EdwinTSalcedo/ForestProtector/images/nighttime-confusion-matrix.png

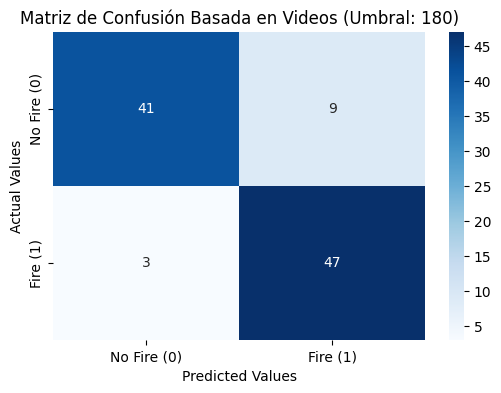
images/nighttime-confusion-matrix.png
