EdwinTSalcedo/ForestProtector/webapp/backend/scripts/captured_frames.gif

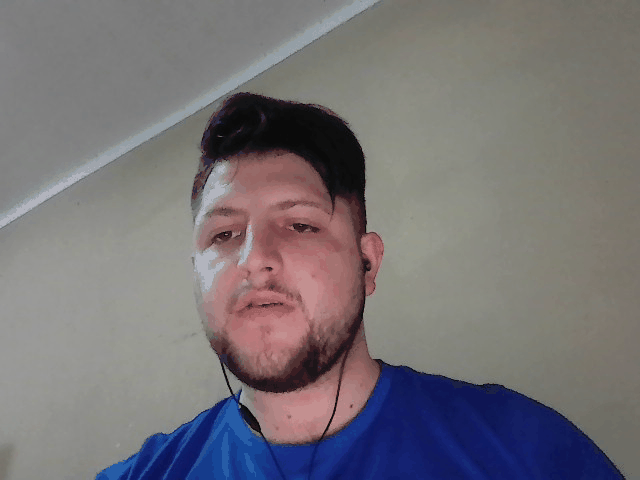
webapp/backend/scripts/captured_frames.gif
