EdwinTSalcedo/ForestProtector/iot_node/cad_files/antenna_ttgo_lora32.SLDASM

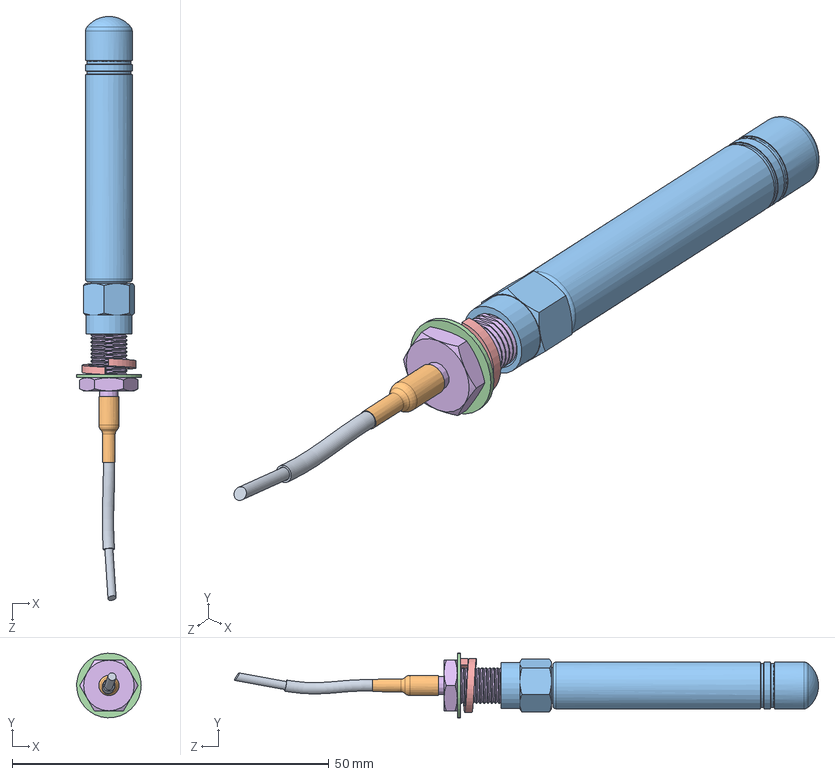
[picture p17: CAD file, 2025-04-28]
iot_node/cad_files/antenna_ttgo_lora32.SLDASM
10.2 x 10.2 x 92.3 mm
antenna_base
antenna_snap_ring
antenna_ring
antenna_flexible
antenna_cover_kabel
antenna_kabel
