EdwinTSalcedo/ForestProtector/iot_node/cad_files/raspberry_pi_pico_r3.SLDASM

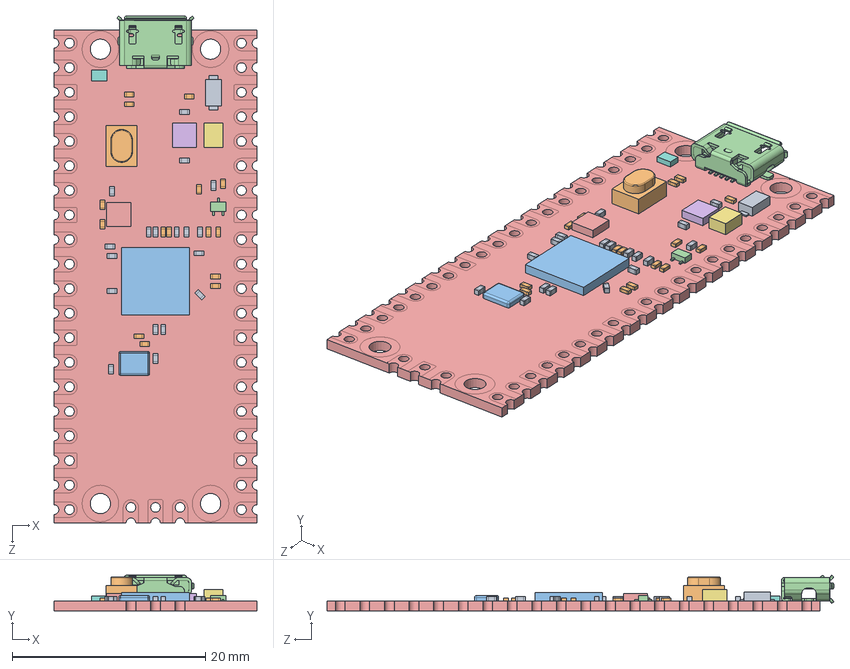
[picture p20: CAD file, 2025-04-28]
iot_node/cad_files/raspberry_pi_pico_r3.SLDASM
21.0 x 3.69 x 52.4 mm
pcb_raspberry_pi_pico_r3
micro_usb_port
rp2040
sw1
d1
d2
l1
u2
u3
q1
x1
smd_resistor x 15
smd_capacitor x 18
