EdwinTSalcedo/ForestProtector/iot_node/cad_files/smd_resistor.SLDPRT

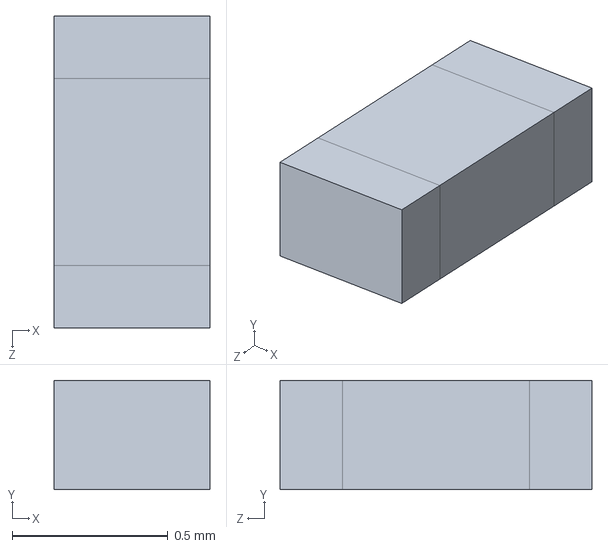
[picture p33: CAD file, 2025-04-26]
iot_node/cad_files/smd_resistor.SLDPRT
0.5 x 0.35 x 1.00 mm
