EdwinTSalcedo/ForestProtector/gateway/3d_printing_files/gateway_enclosure.stl

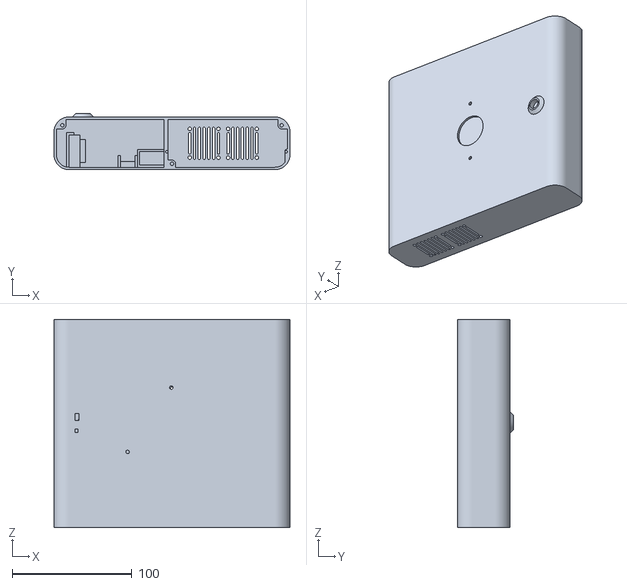
[picture p34: CAD file, 2025-04-26]
gateway/3d_printing_files/gateway_enclosure.stl
197.0 x 47.0 x 174.0
