EdwinTSalcedo/ForestProtector/gateway/cad_files/gateway_parts.SLDPRT

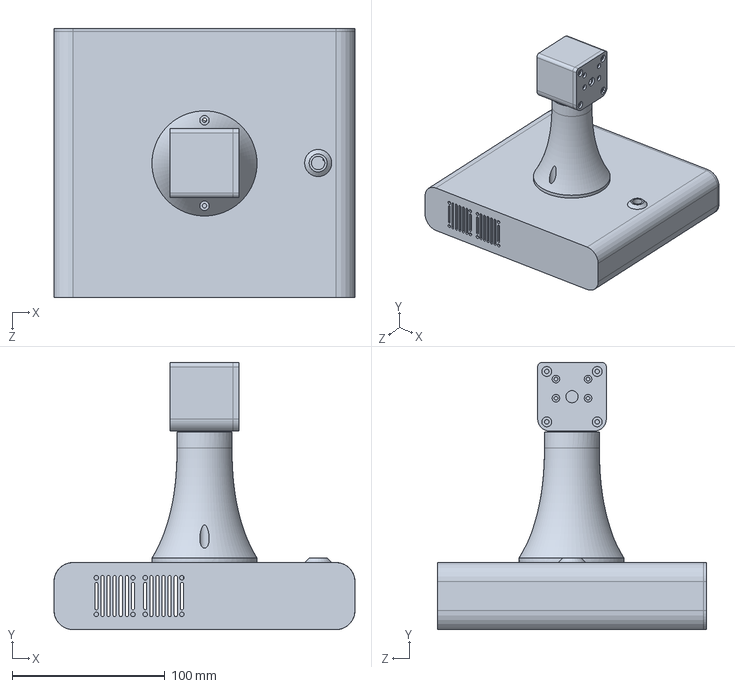
[picture p35: CAD file, 2025-04-26]
gateway/cad_files/gateway_parts.SLDPRT
197.0 x 175.0 x 176.0 mm
