EdwinTSalcedo/ForestProtector/iot_node/3d_printing_files/iot_node_all_parts.3mf

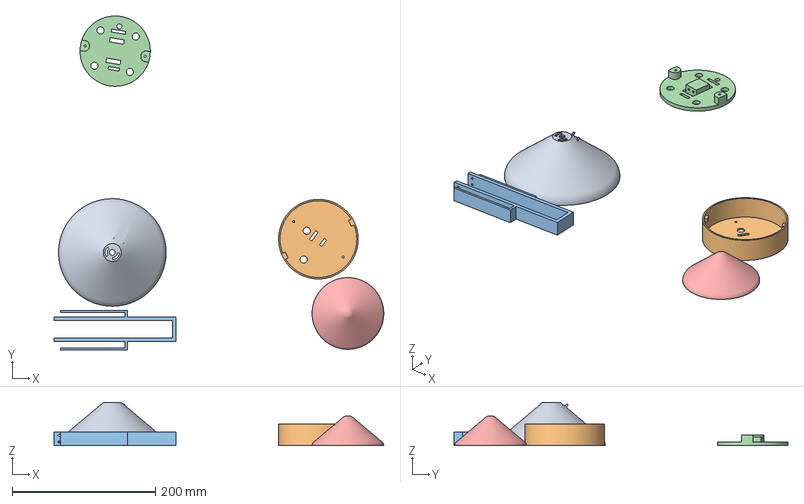
[picture p36: CAD file, 2025-04-26]
iot_node/3d_printing_files/iot_node_all_parts.3mf
459.6 x 465.7 x 60.0 mm
iot_node_lower_canopy.stl
iot_node_main_body.stl
iot_node_power_and_boards_holder.stl
iot_node_sensor_base.stl
iot_node_upper_canopy.stl
