EdwinTSalcedo/ForestProtector/iot_node/cad_files/pcb_raspberry_pi_pico_r3.SLDPRT

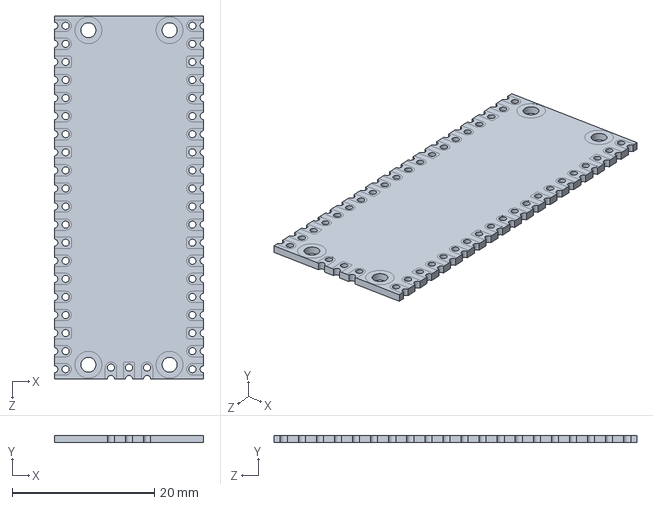
[picture p37: CAD file, 2025-04-26]
iot_node/cad_files/pcb_raspberry_pi_pico_r3.SLDPRT
21.0 x 1.00 x 51.0 mm
