EdwinTSalcedo/ForestProtector/gateway/3d_printing_files/camera_module_cover.stl

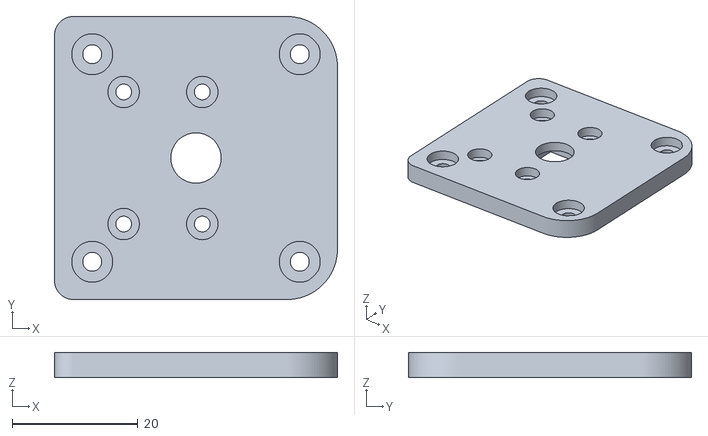
[picture p38: CAD file, 2025-04-26]
gateway/3d_printing_files/camera_module_cover.stl
45.0 x 45.0 x 4.00
