EdwinTSalcedo/ForestProtector/iot_node/3d_printing_files/iot_node_lower_canopy.stl

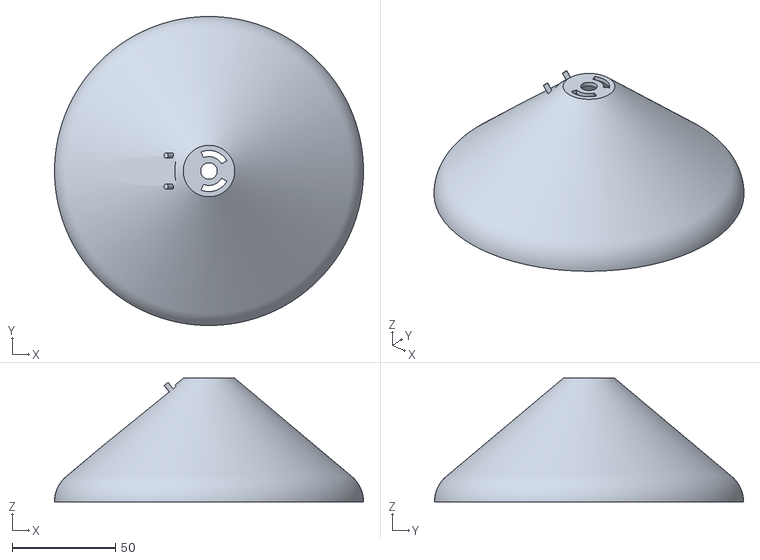
[picture p39: CAD file, 2025-04-26]
iot_node/3d_printing_files/iot_node_lower_canopy.stl
150.0 x 150.0 x 60.0
