EdwinTSalcedo/ForestProtector/iot_node/cad_files/u3.SLDPRT

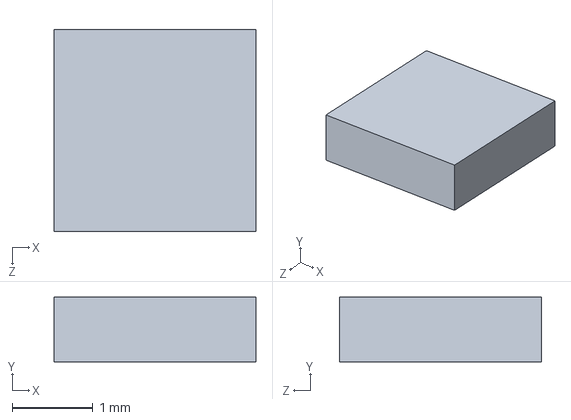
[picture p40: CAD file, 2025-04-26]
iot_node/cad_files/u3.SLDPRT
2.50 x 0.8 x 2.50 mm
