EdwinTSalcedo/ForestProtector/gateway/3d_printing_files/camera_gear_connector.stl

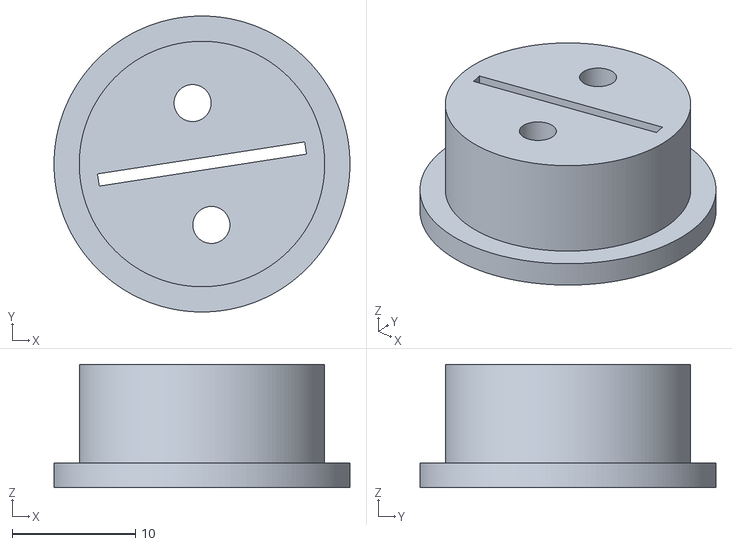
[picture p41: CAD file, 2025-04-26]
gateway/3d_printing_files/camera_gear_connector.stl
24.0 x 24.0 x 10.0
