EdwinTSalcedo/ForestProtector/iot_node/cad_files/pdm_mems.SLDPRT

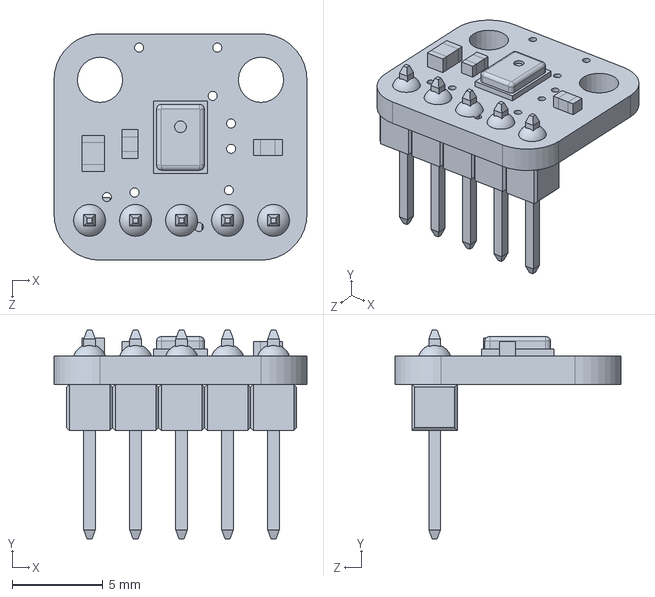
[picture p42: CAD file, 2025-04-26]
iot_node/cad_files/pdm_mems.SLDPRT
14.0 x 11.5 x 12.5 mm
