EdwinTSalcedo/ForestProtector/gateway/3d_printing_files/servo_gear_camera_drive.stl

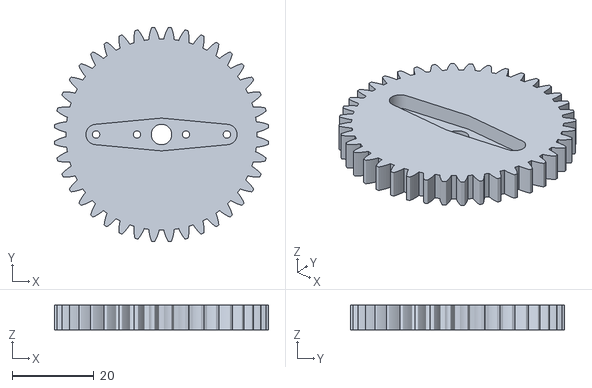
[picture p43: CAD file, 2025-04-26]
gateway/3d_printing_files/servo_gear_camera_drive.stl
52.4 x 52.4 x 6.00
