EdwinTSalcedo/ForestProtector/iot_node/cad_files/mq2.SLDPRT

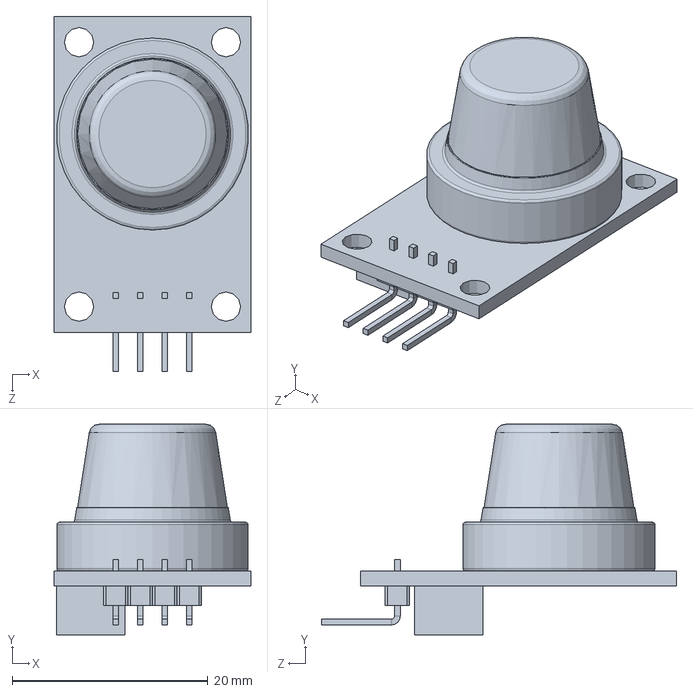
[picture p44: CAD file, 2025-04-26]
iot_node/cad_files/mq2.SLDPRT
20.1 x 21.5 x 36.2 mm
