EdwinTSalcedo/ForestProtector/gateway/3d_printing_files/gateway_all_parts.3mf

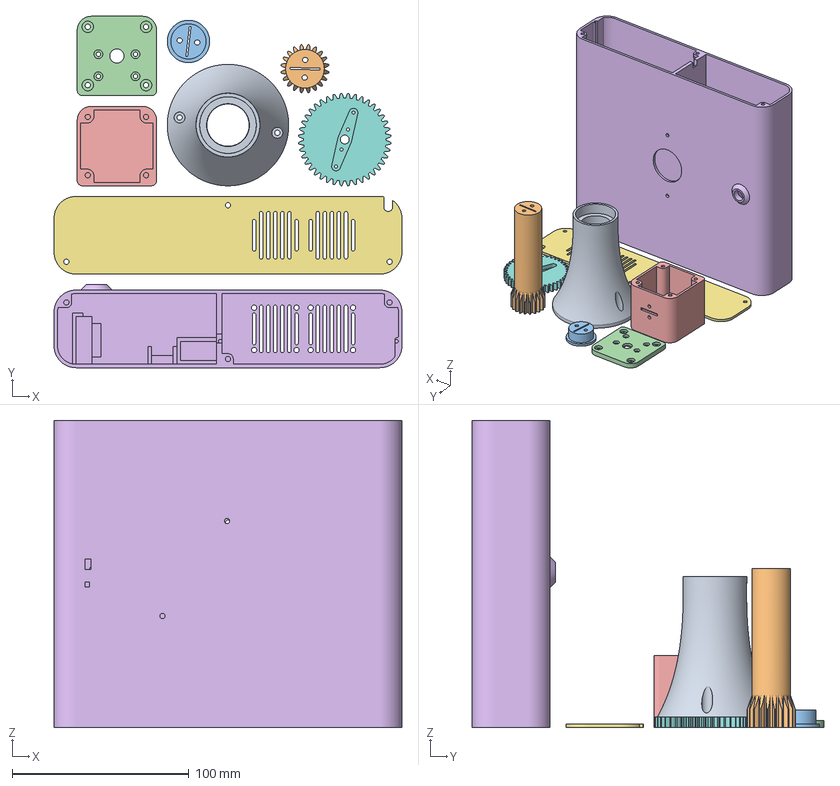
[picture p45: CAD file, 2025-04-26]
gateway/3d_printing_files/gateway_all_parts.3mf
197.0 x 199.0 x 174.0 mm
camera_cable_pillar.stl
camera_gear.stl
camera_gear_connector.stl
camera_module_cover.stl
camera_module_enclosure.stl
gateway_enclosure.stl
gateway_enclosure_cover.stl
servo_gear_camera_drive.stl
