EdwinTSalcedo/ForestProtector/iot_node/cad_files/water_level_sensor.step

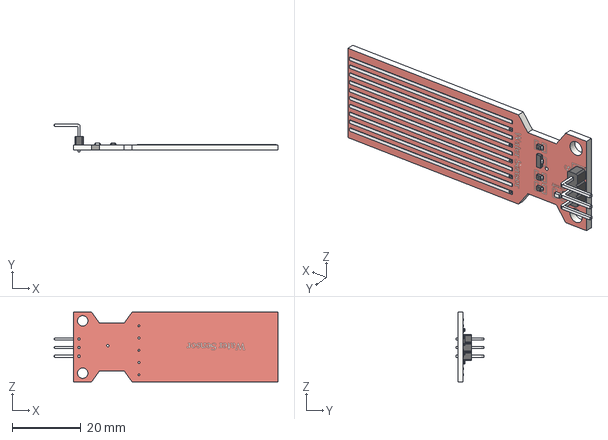
[picture p46: CAD file, 2025-04-26]
iot_node/cad_files/water_level_sensor.step
65.0 x 8.00 x 20.2 mm
