EdwinTSalcedo/ForestProtector/iot_node/cad_files/x1.SLDPRT

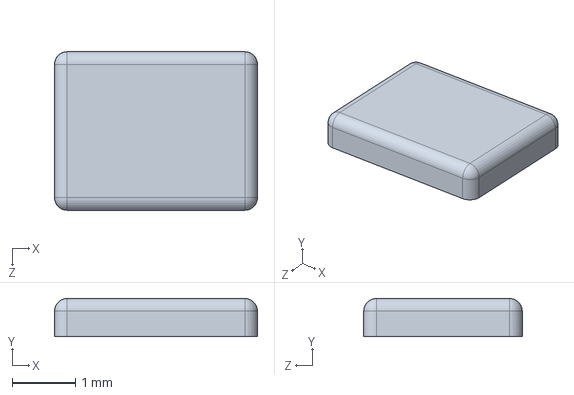
[picture p47: CAD file, 2025-04-26]
iot_node/cad_files/x1.SLDPRT
3.20 x 0.6 x 2.50 mm
