EdwinTSalcedo/ForestProtector/iot_node/cad_files/rp2040.SLDPRT

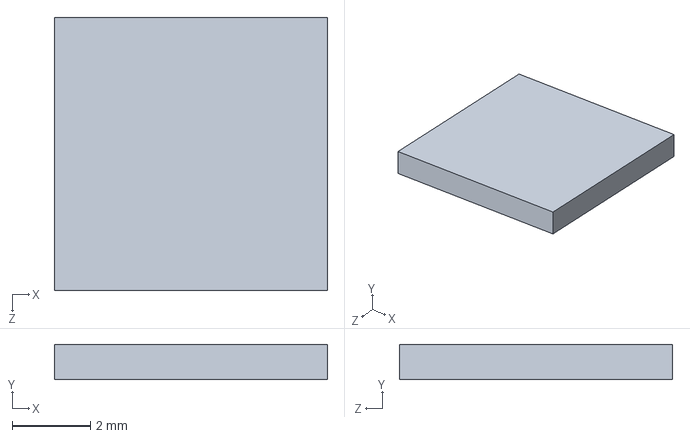
[picture p48: CAD file, 2025-04-26]
iot_node/cad_files/rp2040.SLDPRT
7.00 x 0.9 x 7.00 mm
