EdwinTSalcedo/ForestProtector/iot_node/cad_files/l1.SLDPRT

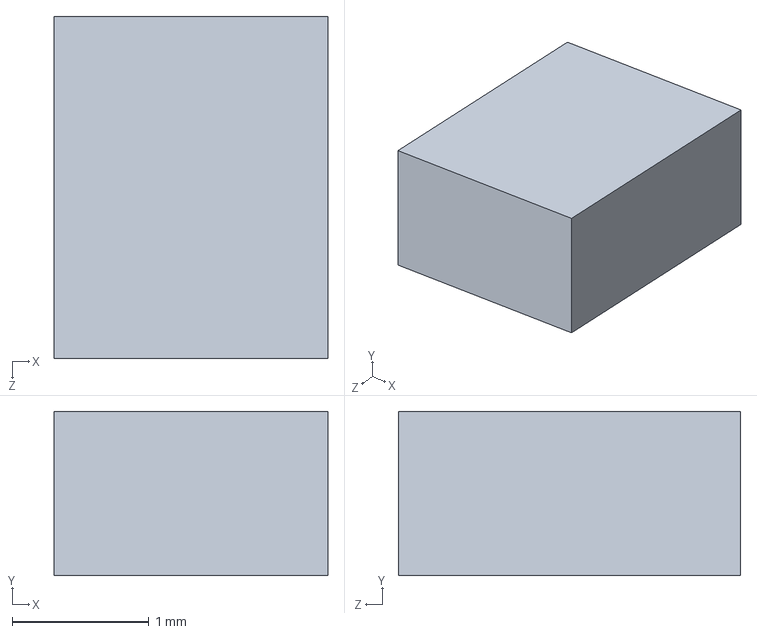
[picture p49: CAD file, 2025-04-26]
iot_node/cad_files/l1.SLDPRT
2.00 x 1.20 x 2.50 mm
