EdwinTSalcedo/ForestProtector/iot_node/cad_files/sw1.SLDPRT

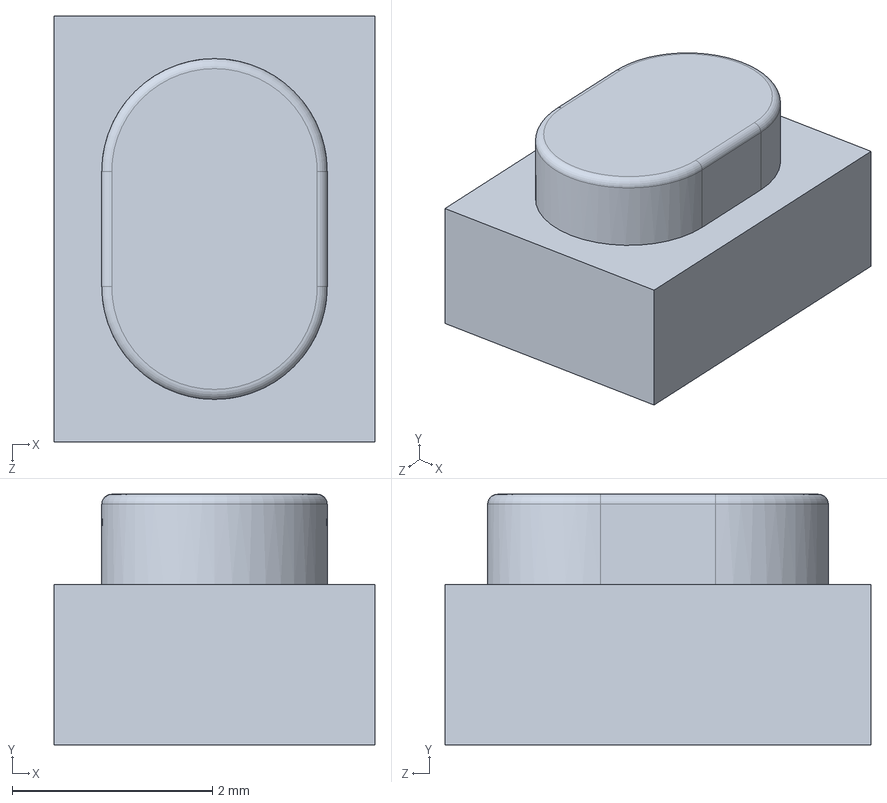
[picture p50: CAD file, 2025-04-26]
iot_node/cad_files/sw1.SLDPRT
3.20 x 2.50 x 4.25 mm
