EdwinTSalcedo/ForestProtector/iot_node/cad_files/micro_usb_port.SLDPRT

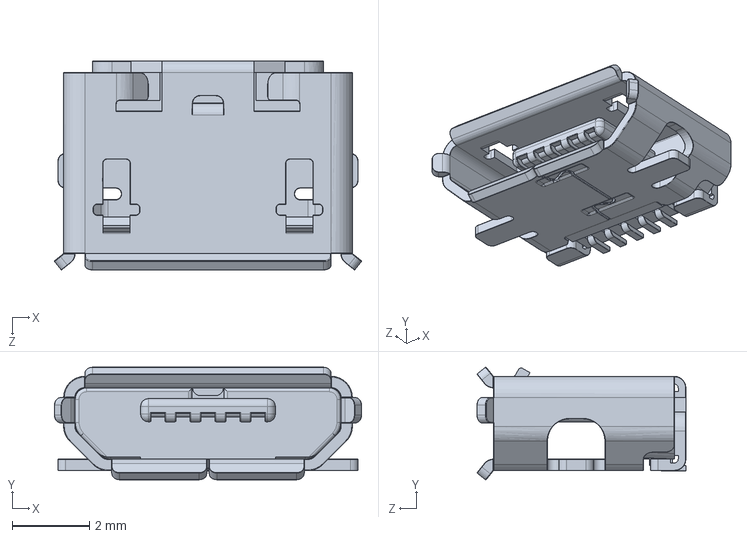
[picture p51: CAD file, 2025-04-26]
iot_node/cad_files/micro_usb_port.SLDPRT
7.97 x 2.92 x 5.43 mm
