EdwinTSalcedo/ForestProtector/iot_node/cad_files/q1.SLDPRT

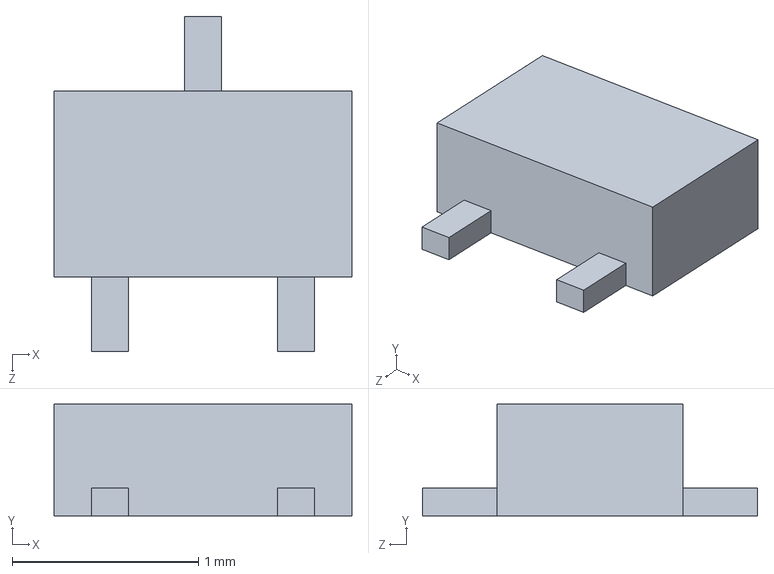
[picture p52: CAD file, 2025-04-26]
iot_node/cad_files/q1.SLDPRT
1.60 x 0.6 x 1.80 mm
