EdwinTSalcedo/ForestProtector/iot_node/cad_files/smd_capacitor.SLDPRT

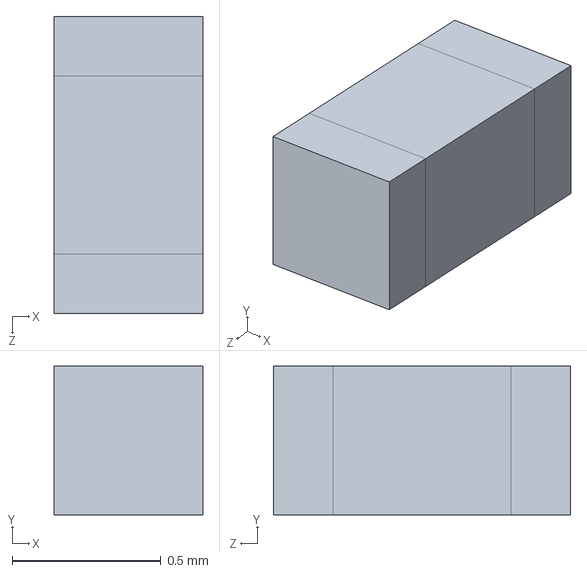
[picture p53: CAD file, 2025-04-26]
iot_node/cad_files/smd_capacitor.SLDPRT
0.5 x 0.5 x 1.00 mm
