EdwinTSalcedo/ForestProtector/iot_node/cad_files/antenna_cover_kabel.SLDPRT

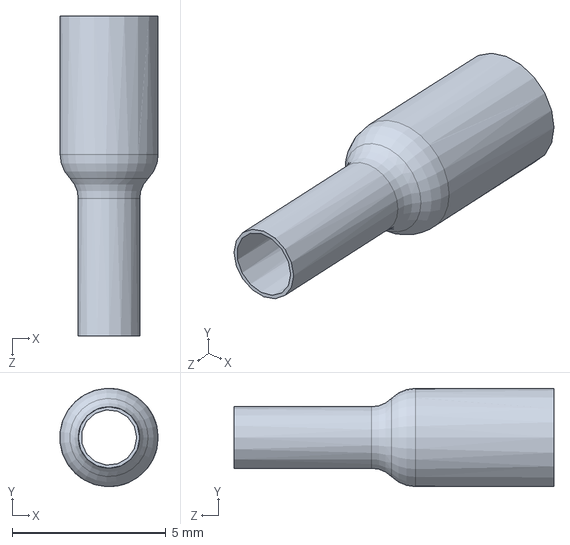
[picture p54: CAD file, 2025-04-26]
iot_node/cad_files/antenna_cover_kabel.SLDPRT
3.20 x 3.20 x 10.4 mm
