EdwinTSalcedo/ForestProtector/iot_node/cad_files/antenna_base.SLDPRT

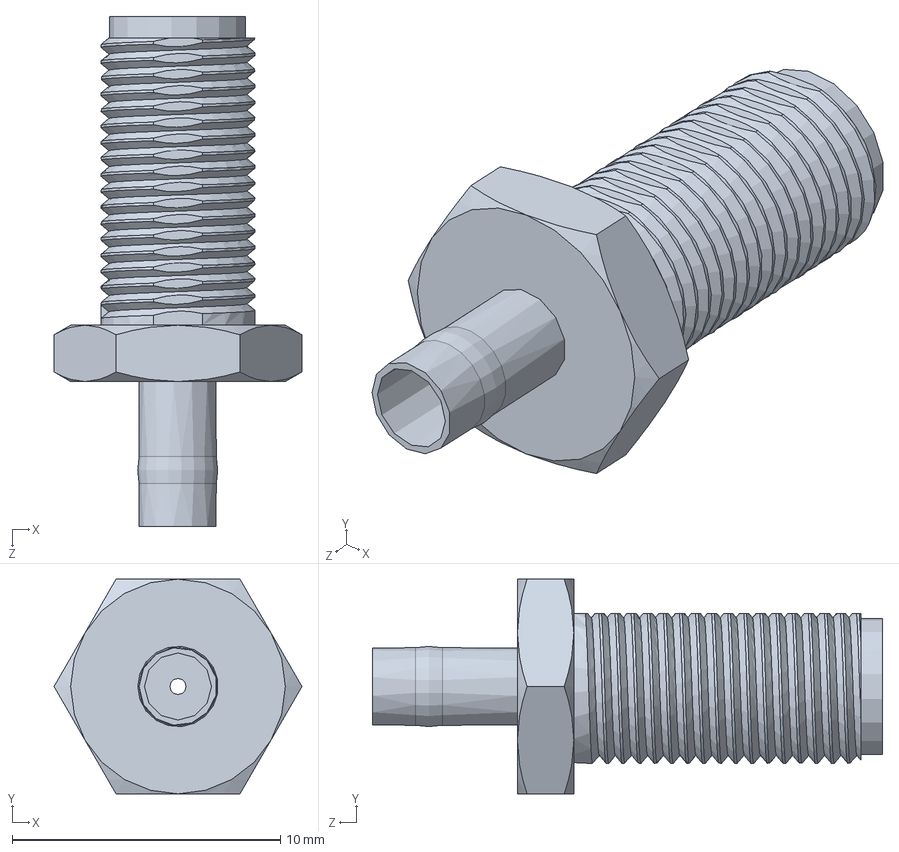
[picture p55: CAD file, 2025-04-26]
iot_node/cad_files/antenna_base.SLDPRT
9.24 x 8.00 x 19.0 mm
