EdwinTSalcedo/ForestProtector/iot_node/cad_files/antenna_kabel.SLDPRT

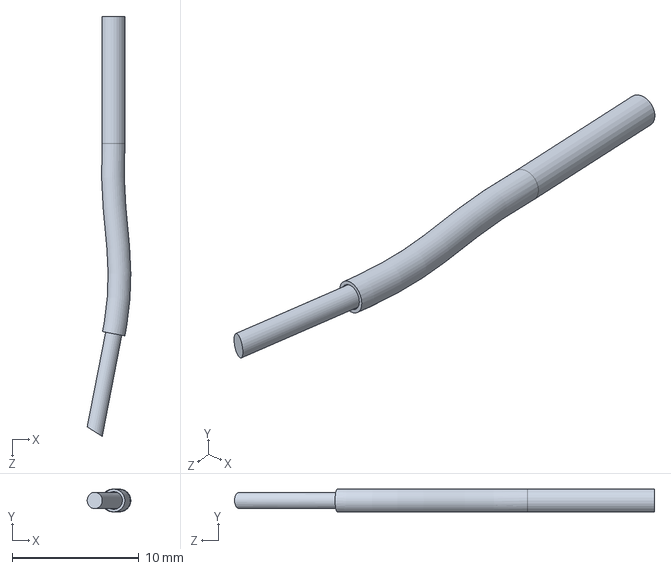
[picture p56: CAD file, 2025-04-26]
iot_node/cad_files/antenna_kabel.SLDPRT
3.44 x 1.80 x 33.1 mm
