EdwinTSalcedo/ForestProtector/iot_node/cad_files/bme280.SLDPRT

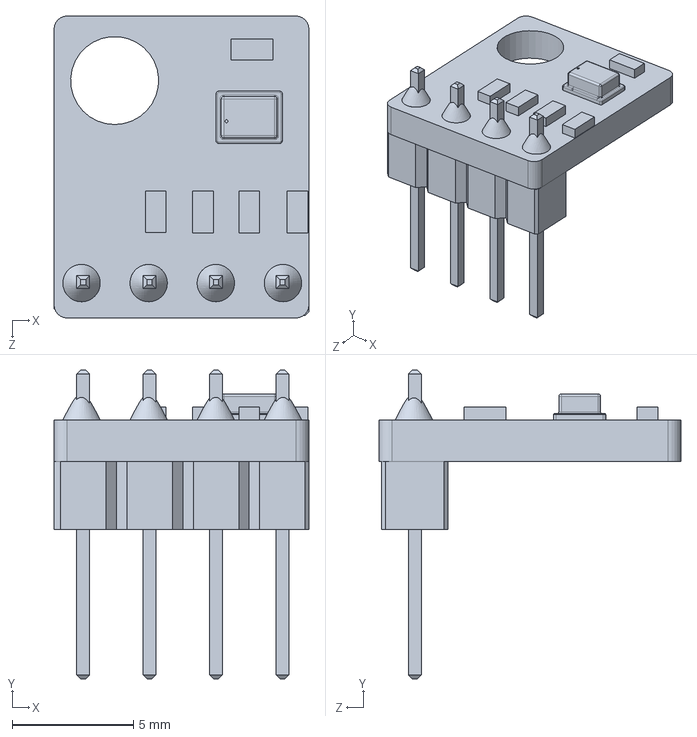
[picture p57: CAD file, 2025-04-26]
iot_node/cad_files/bme280.SLDPRT
10.5 x 12.7 x 12.4 mm
