EdwinTSalcedo/ForestProtector/iot_node/cad_files/antenna_flexible.SLDPRT

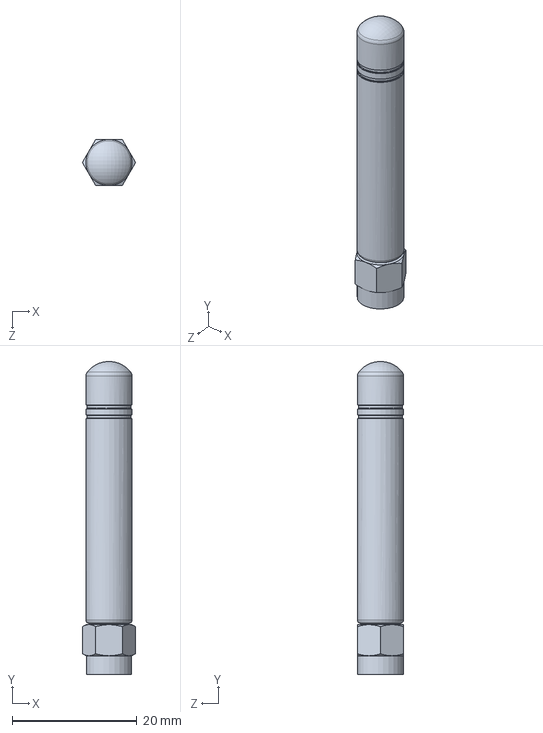
[picture p58: CAD file, 2025-04-26]
iot_node/cad_files/antenna_flexible.SLDPRT
8.54 x 50.2 x 7.40 mm
