EdwinTSalcedo/ForestProtector/iot_node/cad_files/antenna_ring.SLDPRT

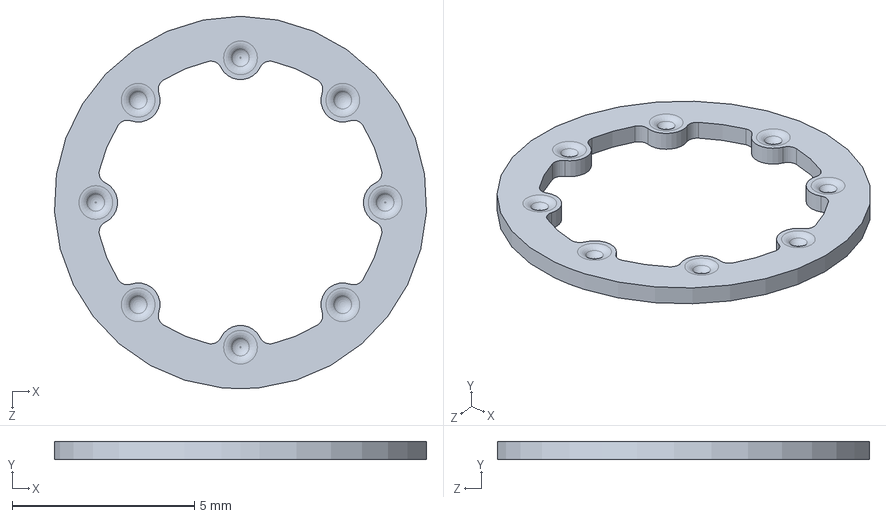
[picture p59: CAD file, 2025-04-26]
iot_node/cad_files/antenna_ring.SLDPRT
10.2 x 0.5 x 10.2 mm
