EdwinTSalcedo/ForestProtector/iot_node/cad_files/design1.SLDPRT

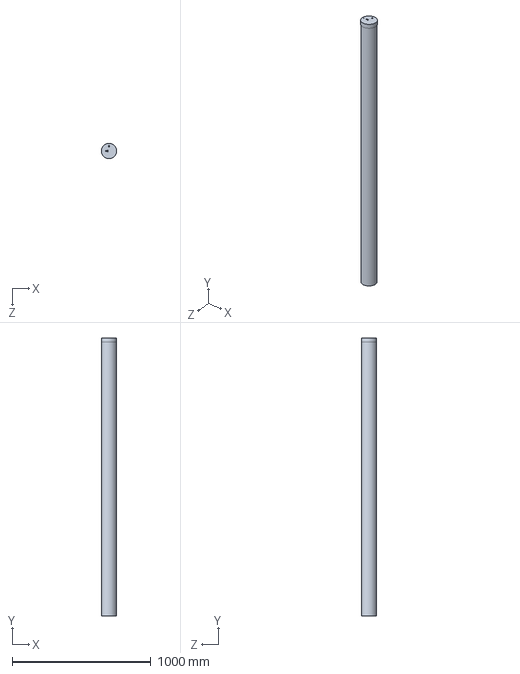
[picture p60: CAD file, 2025-04-26]
iot_node/cad_files/design1.SLDPRT
111.0 x 2002.5 x 111.0 mm
