EdwinTSalcedo/ForestProtector/iot_node/cad_files/pin_header1x20solder.SLDPRT

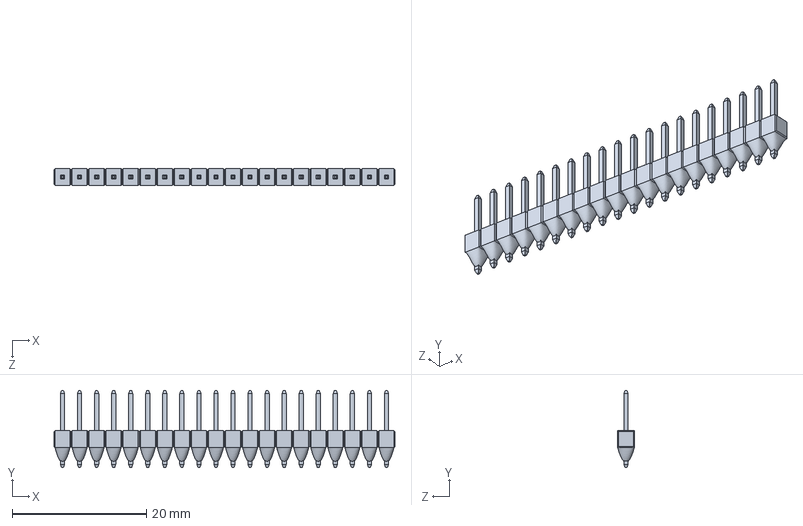
[picture p61: CAD file, 2025-04-26]
iot_node/cad_files/pin_header1x20solder.SLDPRT
50.8 x 11.5 x 2.50 mm
