EdwinTSalcedo/ForestProtector/iot_node/cad_files/d2.SLDPRT

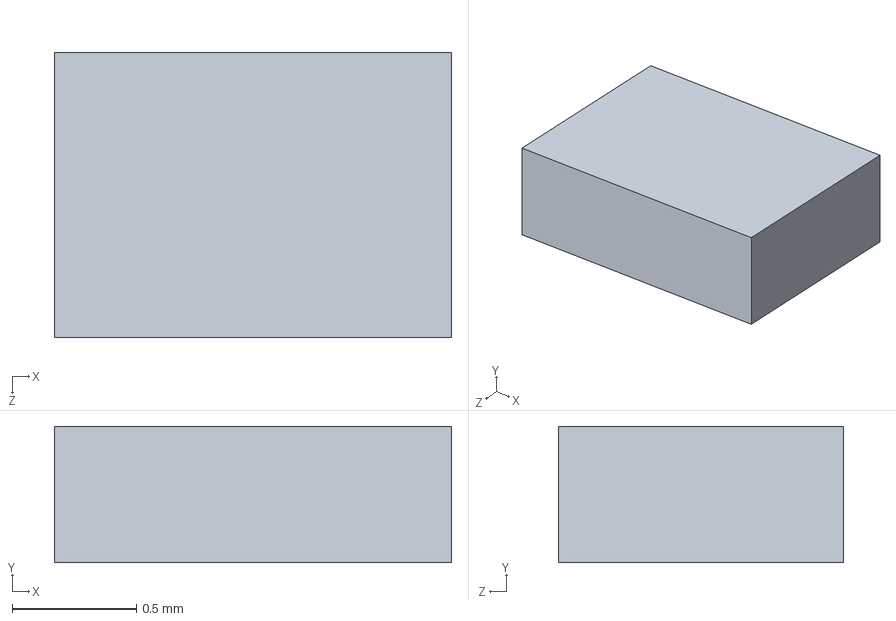
[picture p62: CAD file, 2025-04-26]
iot_node/cad_files/d2.SLDPRT
1.60 x 0.55 x 1.15 mm
