EdwinTSalcedo/ForestProtector/iot_node/cad_files/antenna_snap_ring.SLDPRT

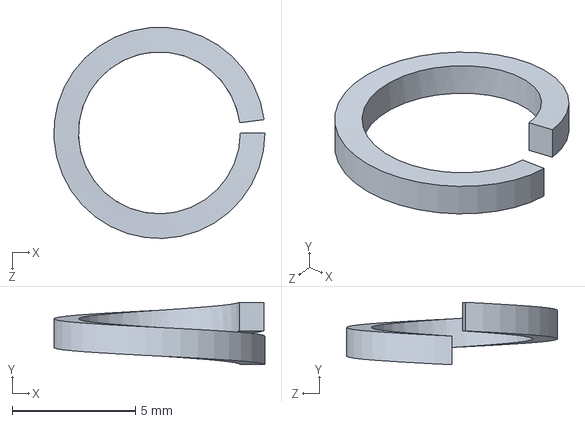
[picture p63: CAD file, 2025-04-26]
iot_node/cad_files/antenna_snap_ring.SLDPRT
8.55 x 2.53 x 8.55 mm
