EdwinTSalcedo/ForestProtector/iot_node/cad_files/d1.SLDPRT

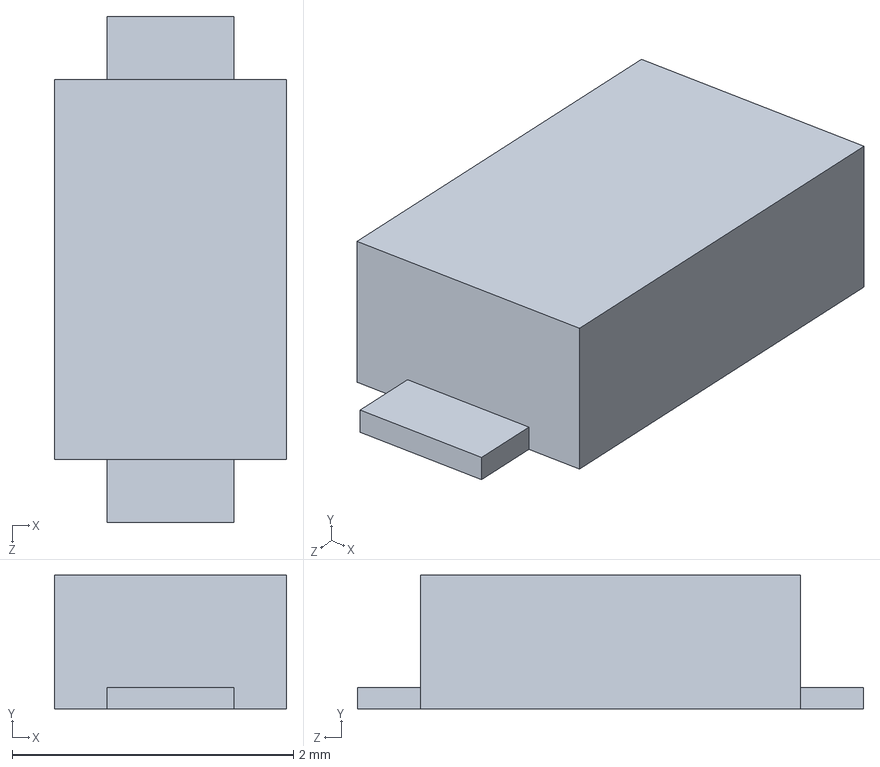
[picture p64: CAD file, 2025-04-26]
iot_node/cad_files/d1.SLDPRT
1.65 x 0.95 x 3.60 mm
